morfredus/MeteoHubSensor/include/board_config.h

#pragma once
#include <Arduino.h>

// ============================================================================
// Brochage MeteoHubSensor - ESP32-S3 Super Mini
// ============================================================================
// Cible unique (env sonde-supermini, define SENSOR_BOARD_S3). Le reste du firmware ne
// connait que les alias PIN_* et le drapeau SENSOR_NEEDS_TX_LIMIT : ajouter une
// autre carte se ferait ici, sans toucher aux modules. (La cible C3 HW-675 a ete
// retiree, et avec elle le module d'ecran OLED qui ne servait qu'a elle.)
// ============================================================================

// ---------------------------------------------------------------------------
// ESP32-S3 Super Mini (LED RGB seule, sans ecran)
// ---------------------------------------------------------------------------
// USB natif : GPIO 19/20. BOOT : GPIO 0 (non sorti). Straps : 45/46.
// LED RGB onboard : GPIO 48 (GPIO 46 = input-only, ignore malgre le pinout).
constexpr char BOARD_NAME[] = "ESP32-S3 Super Mini";

// --- Module BMP280 (0x77) + AHT20 (0x38) : seule la pression du BMP280 est utilisee ---
// Cablage : fil SDA du module -> GP8, fil SCL du module -> GP9, 3V3, GND.
constexpr uint8_t PIN_SENSOR_SDA = 8;
constexpr uint8_t PIN_SENSOR_SCL = 9;
constexpr int8_t PIN_SENSOR_POWER = -1; // -1 = alim 3V3 permanente

// LED RGB onboard.
constexpr int8_t PIN_LED_RGB = 48;
constexpr uint8_t NUM_PIXELS = 1;

// Bouton BOOT.
constexpr uint8_t PIN_BOOT_BUTTON = 0;

// Alimentation : module regulateur Youmi 3,3 V (entree annoncee 4,5-7 V) + accu Li-ion
// 3,7 V (3000 mAh depuis le 2026-10-03), charge dans un chargeur de bureau (pas de
// charge USB) ; deux accus a permuter. Il a remplace le module Breadvolt (boost, protection decharge
// 2,4 V / charge 4,28 V) qui decrochait en deep sleep. Le 3,3 V regule est CONSTANT :
// le mesurer ne dirait rien de l'accu. On tape donc la CELLULE, AVANT le
// regulateur, au + de l'accu (multimetre ~4,0 V en charge).
//
// Cablage batterie (2026-09-15) : + accu --[R1 100k]--(GP4)--[R2 100k]-- GND.
// GP4 lit le point milieu = tension accu / 2 (~2,0 V pour 4,0 V), sous la limite
// ADC du S3 : indispensable, l'accu monte a 4,28 V en pleine charge et ne doit
// JAMAIS arriver brut sur la pin. Le firmware remultiplie par le ratio du pont
// (BATTERY_DIVIDER_RATIO = 2,0 dans config.h). Le pont draine en continu
// ~4,0 V / 200 k = 20 uA, negligeable devant les reveils TX. La plage Li-ion
// 2,6-4,2 ci-dessous convertit en pourcentage.
constexpr int8_t PIN_BATTERY_ADC = 4;
// Bornes de la plage de PLAUSIBILITE de la lecture (garde de power_manager.cpp, +/- 0,5 V) :
// elles ne servent plus au pourcentage, calcule par la courbe Li-ion de battery_curve.h.
// 2,6 V = 0,2 V au-dessus de la coupure 2,4 V de l'ancien Breadvolt : une pile presque
// vide doit encore etre signalee, pas rejetee. Sous ~3,0 V la courbe Li-ion s'effondre.
constexpr float BATTERY_VOLTAGE_MIN = 2.6f;
constexpr float BATTERY_VOLTAGE_MAX = 4.2f; // Li-ion pleine charge
// Facteur de calibration fin propre a CE S3 + CE pont (voir config.h).
// Accu Li-ion 3,7 V 3000 mAh, 2026-10-03. Releves multimetre / sonde (facteur 1,0515 pose) :
//   3,927 V / 3,98 V rapportes  -> facteur reel 1,0377
//   4,074 V / 4,14 V rapportes  -> facteur reel 1,0347      moyenne retenue : 1,036
// Le premier releve (3,859 V pour 3,67 V avec l'ancien firmware, soit 1,0515) s'ecarte de
// 1,5 % : mesure non simultanee, accu fraichement sorti du chargeur. Residu avec 1,036 :
// -0,2 % et +0,1 % sur les deux points retenus. L'ecart tient surtout a l'impedance du pont
// 100k/100k (50 kohm vue par l'ADC) ; il est proportionnel a la tension. A reverifier
// a pleine charge stable (~4,2 V) et a mi-charge ; un condensateur 100 nF GP4-GND
// rendrait la lecture plus juste et plus stable. Reposer : facteur = actuel x Vmultimetre / Vlu.
constexpr float BATTERY_VREF_CALIBRATION = 1.036f;

// --- DHT22 : reference temperature ET humidite (calibre en sel sature a 75 %, voir docs/notes.md) ---
// Fil DATA -> GP1, 3V3, GND (module 3 broches : resistance de rappel deja presente ; DHT22 nu : 10 k vers 3V3).
constexpr uint8_t PIN_DHT22 = 1;
// Correctifs de calibration (ajoutes a la lecture). Sel sature NaCl : 75,0 a 75,1 % pendant 2 h -> 0.
constexpr float DHT22_HUM_OFFSET = 0.0f;
constexpr float DHT22_TEMP_OFFSET = 0.0f;

// --- Reserves meteo ---
constexpr uint8_t PIN_ANEMOMETER_PULSE = 5; // deplace de GP1 (0.30.0) : GP1 sert au DHT22
constexpr uint8_t PIN_WIND_VANE_ADC = 2;
constexpr uint8_t PIN_RAIN_GAUGE_PULSE = 7;
constexpr uint8_t PIN_AUX_ADC = 10;
constexpr uint8_t PIN_FREE_GP6 = 6;

// Pas d'ecran : le statut passe par la LED RGB seule. Un ecran eventuellement
// cable mais jamais initialise reste dans son etat reset basse conso.

// Plafond TX ESP-NOW sur le S3 (2026-09-14). Preuve terrain (logs USB, firmware
// 0.13.0 unicast) : a pleine puissance, le S3 emet mais le hub ne renvoie PAS
// d'ACK (NACK a tous les essais). L'antenne PCB du S3 Super Mini est mal adaptee :
// trop de puissance = signal trop degrade pour etre acquitte. On plafonne donc,
// valeur reglee dans config.h (SENSOR_TX_POWER_LEVEL), a remonter progressivement
// (menu config.h) pour retrouver le maximum de portee qui reste stable.
#define SENSOR_NEEDS_TX_LIMIT 1

// Alias I2C (meme bus, memes GPIO).
constexpr uint8_t PIN_I2C_SDA = PIN_SENSOR_SDA;
constexpr uint8_t PIN_I2C_SCL = PIN_SENSOR_SCL;
