morfredus/MeteoHubSensor/src/modules/power_manager.cpp

#include "power_manager.h"
#include "battery_curve.h"
#include <esp_sleep.h>
#include <driver/rtc_io.h>
#include <sys/time.h>
#include <WiFi.h>

PowerManager::PowerManager() 
    : _pixel(NUM_PIXELS, PIN_LED_RGB, NEO_GRB + NEO_KHZ800) {}

void PowerManager::begin() {
    // LED RGB onboard (WS2812 sur GPIO 48)
    if (PIN_LED_RGB >= 0) {
        _pixel.begin();
        _pixel.setBrightness(30); // Luminosité douce pour ne pas éblouir ni trop consommer
        _pixel.clear();
        _pixel.show();
        _pixelReady = true;
    }

    // ADC batterie (GPIO 4, ADC1). Quelques lectures a vide : la 1re
    // analogReadMilliVolts apres boot sort souvent Vref=0.
    if (PIN_BATTERY_ADC >= 0) {
        pinMode(PIN_BATTERY_ADC, INPUT);
        analogReadResolution(12);
        analogSetPinAttenuation(PIN_BATTERY_ADC, ADC_11db);
        for (uint8_t i = 0; i < 8; i++) {
            (void)analogReadMilliVolts(PIN_BATTERY_ADC);
            delay(2);
        }
    }
}

void PowerManager::setLedColor(uint8_t r, uint8_t g, uint8_t b) {
    if (!_pixelReady) return;
    _pixel.setPixelColor(0, _pixel.Color(r, g, b));
    _pixel.show();
}

void PowerManager::turnOffLed() {
    if (!_pixelReady) return;
    _pixel.clear();
    _pixel.show();
}

void PowerManager::blinkStatus(uint8_t r, uint8_t g, uint8_t b, uint16_t durationMs) {
    if (!_pixelReady) return;
    setLedColor(r, g, b);
    delay(durationMs);
    turnOffLed();
}

void PowerManager::readBattery(MeteoPacket& packet) {
    if (PIN_BATTERY_ADC < 0) {
        packet.battery_voltage = 0.0f;
        packet.battery_percent = 0;
        return;
    }

    // Moyennage sur 16 échantillons pour lisser le bruit ADC
    uint32_t adcSum = 0;
    constexpr uint8_t SAMPLES = 16;
    for (uint8_t i = 0; i < SAMPLES; i++) {
        adcSum += analogReadMilliVolts(PIN_BATTERY_ADC);
        delayMicroseconds(200);
    }
    
    float pinMilliVolts = (float)adcSum / (float)SAMPLES;
    
    // Tension réelle batterie (V) = tension broche (V) * ratio diviseur * calibration
    float rawVoltage = (pinMilliVolts / 1000.0f) * BATTERY_DIVIDER_RATIO * BATTERY_VREF_CALIBRATION;
    
    _lastVoltage = rawVoltage;

    // Pourcentage : courbe de charge Li-ion par paliers (include/battery_curve.h), et
    // non une droite BATTERY_VOLTAGE_MIN-MAX qui surestimait fortement vers 3,7 V.
    _lastPercent = mhbatt::liIonPercent(_lastVoltage);

    // Garde de plausibilite : rejette une lecture aberrante (pont absent, pin
    // flottant) SANS masquer une pile reellement faible. On borne donc autour de
    // la plage de la CARTE (BATTERY_VOLTAGE_MIN/MAX, chimie-dependante) avec une
    // marge : une pile presque vide (proche de MIN) doit encore etre signalee.
    constexpr float kGuardMargin = 0.5f;
    if (_lastVoltage < (BATTERY_VOLTAGE_MIN - kGuardMargin)
        || _lastVoltage > (BATTERY_VOLTAGE_MAX + kGuardMargin)) {
        packet.battery_voltage = 0.0f;
        packet.battery_percent = 0;
        Serial.printf("[POWER] Batterie ignoree (%.2f V) : hors plage carte [%.1f-%.1f V]\n",
                      _lastVoltage, BATTERY_VOLTAGE_MIN, BATTERY_VOLTAGE_MAX);
        return;
    }

    packet.battery_voltage = _lastVoltage;
    packet.battery_percent = _lastPercent;
    packet.valid_fields |= FIELD_BATTERY;

    Serial.printf("[POWER] Batterie: %.2f V (%d %%)\n", _lastVoltage, _lastPercent);
}

// Heure (horloge système, maintenue par le RTC à travers le deep sleep) du
// prochain réveil programmé, en µs. 0 = inconnue.
RTC_DATA_ATTR static int64_t rtcScheduledWakeUs = 0;

static int64_t nowUs() {
    struct timeval tv;
    gettimeofday(&tv, nullptr);
    return (int64_t)tv.tv_sec * 1000000LL + tv.tv_usec;
}

uint32_t PowerManager::secondsUntilScheduledWake() const {
    if (rtcScheduledWakeUs == 0) return 0;
    const int64_t left = rtcScheduledWakeUs - nowUs();
    if (left <= 0) return 0;
    // Borne de sécurité : jamais plus d'un intervalle (horloge recalée entre-temps).
    const int64_t maxUs = (int64_t)SENSOR_MEASUREMENT_INTERVAL_SECONDS * 1000000LL;
    return (uint32_t)((left < maxUs ? left : maxUs) / 1000000LL);
}

void PowerManager::enterDeepSleep(uint32_t seconds) {
    Serial.printf("[POWER] Mise en veille profonde (Deep Sleep) pour %u secondes...\n", seconds);
    Serial.flush();

    // Extinction complète de la LED RGB avant sommeil
    turnOffLed();

    // Configuration du réveil par timer
    esp_sleep_enable_timer_wakeup((uint64_t)seconds * 1000000ULL);
    rtcScheduledWakeUs = nowUs() + (int64_t)seconds * 1000000LL;

    // Réveil par le bouton BOOT (niveau bas = appuyé), pour l'appairage. ext0
    // garde le domaine RTC alimenté, ce qui permet le pull-up interne pendant le
    // sommeil (quelques µA de plus, négligeable devant les réveils radio).
    // Armé SEULEMENT si le bouton est au repos maintenant : un bouton coincé
    // (ou GPIO0 tiré à la masse par l'humidité) réveillerait la sonde en boucle,
    // sans mesure. Il sera réarmé au premier sommeil où GPIO0 est revenu haut.
    if (digitalRead(PIN_BOOT_BUTTON) == HIGH) {
        rtc_gpio_pullup_en((gpio_num_t)PIN_BOOT_BUTTON);
        rtc_gpio_pulldown_dis((gpio_num_t)PIN_BOOT_BUTTON);
        esp_sleep_enable_ext0_wakeup((gpio_num_t)PIN_BOOT_BUTTON, 0);
    } else {
        Serial.println("[POWER] [WARN] BOOT au niveau bas : reveil par bouton non arme");
        Serial.flush();
    }
    
    // Extinction du Wi-Fi avant sommeil
    WiFi.disconnect(true);
    WiFi.mode(WIFI_OFF);
    
    esp_deep_sleep_start();
}
